dilshan/6ch-sound-processor/6ch-sound-fx-controller/src/resources.c

#include <gio/gio.h>

#if defined (__ELF__) && ( __GNUC__ > 2 || (__GNUC__ == 2 && __GNUC_MINOR__ >= 6))
# define SECTION __attribute__ ((section (".gresource.ch_tone_control"), aligned (8)))
#else
# define SECTION
#endif

#ifdef _MSC_VER
static const SECTION union { const guint8 data[22413]; const double alignment; void * const ptr;}  ch_tone_control_resource_data = { {
  0107, 0126, 0141, 0162, 0151, 0141, 0156, 0164, 0000, 0000, 0000, 0000, 0000, 0000, 0000, 0000, 
  0030, 0000, 0000, 0000, 0254, 0000, 0000, 0000, 0000, 0000, 0000, 0050, 0005, 0000, 0000, 0000, 
  0000, 0000, 0000, 0000, 0001, 0000, 0000, 0000, 0002, 0000, 0000, 0000, 0003, 0000, 0000, 0000, 
  0004, 0000, 0000, 0000, 0324, 0265, 0002, 0000, 0377, 0377, 0377, 0377, 0254, 0000, 0000, 0000, 
  0001, 0000, 0114, 0000, 0260, 0000, 0000, 0000, 0264, 0000, 0000, 0000, 0215, 0256, 0131, 0076, 
  0003, 0000, 0000, 0000, 0264, 0000, 0000, 0000, 0007, 0000, 0166, 0000, 0300, 0000, 0000, 0000, 
  0152, 0127, 0000, 0000, 0302, 0257, 0211, 0013, 0000, 0000, 0000, 0000, 0152, 0127, 0000, 0000, 
  0004, 0000, 0114, 0000, 0160, 0127, 0000, 0000, 0164, 0127, 0000, 0000, 0103, 0254, 0277, 0142, 
  0004, 0000, 0000, 0000, 0164, 0127, 0000, 0000, 0007, 0000, 0114, 0000, 0174, 0127, 0000, 0000, 
  0200, 0127, 0000, 0000, 0024, 0075, 0271, 0274, 0002, 0000, 0000, 0000, 0200, 0127, 0000, 0000, 
  0010, 0000, 0114, 0000, 0210, 0127, 0000, 0000, 0214, 0127, 0000, 0000, 0057, 0000, 0000, 0000, 
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
  "\000\031\164\105\130\164\123\157\146\164\167\141\162\145\000\167"
  "\167\167\056\151\156\153\163\143\141\160\145\056\157\162\147\233"
  "\356\074\032\000\000\040\000\111\104\101\124\170\234\354\235\167"
  "\170\134\305\271\270\337\355\105\132\365\056\331\226\254\342\046"
  "\313\105\256\340\202\301\066\275\044\100\022\002\111\110\041\044"
  "\067\067\355\246\367\033\322\313\057\275\020\222\134\040\215\164"
  "\010\020\212\301\306\275\127\331\226\055\313\226\255\336\173\335"
  "\172\176\177\034\213\030\133\147\316\356\352\154\223\367\175\236"
  "\175\300\072\263\063\263\273\347\373\316\314\067\137\321\161\165"
  "\220\016\254\003\126\003\163\201\122\040\011\110\001\164\021\234"
  "\127\234\310\043\001\175\300\000\120\013\124\003\333\201\255\100"
  "\167\344\246\025\147\262\350\201\273\201\177\003\156\344\037\072"
  "\376\212\277\374\175\271\201\347\201\067\043\337\113\161\142\004"
  "\035\360\166\240\206\310\337\104\361\327\324\170\235\002\336\106"
  "\234\250\247\030\170\215\310\337\060\361\327\324\174\155\006\212"
  "\210\023\225\334\203\274\227\213\364\115\022\177\115\355\127\057"
  "\360\046\246\010\206\110\117\100\043\076\002\374\006\260\105\172"
  "\042\161\246\074\126\340\055\300\010\260\073\302\163\231\064\123"
  "\101\001\174\036\370\036\161\153\176\234\360\241\003\066\000\116"
  "\140\147\204\347\062\051\142\135\150\336\013\374\232\000\076\207"
  "\303\142\142\132\262\035\207\305\104\212\325\114\222\335\206\121"
  "\037\067\362\136\255\110\100\357\310\030\275\243\116\316\164\366"
  "\323\067\352\014\364\355\357\001\236\010\305\334\302\101\054\053"
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
#endif /* !_MSC_VER */

static GStaticResource static_resource = { ch_tone_control_resource_data.data, sizeof (ch_tone_control_resource_data.data) - 1 /* nul terminator */, NULL, NULL, NULL };

G_MODULE_EXPORT
GResource *ch_tone_control_get_resource (void);
GResource *ch_tone_control_get_resource (void)
{
  return g_static_resource_get_resource (&static_resource);
}
/*
  If G_HAS_CONSTRUCTORS is true then the compiler support *both* constructors and
  destructors, in a usable way, including e.g. on library unload. If not you're on
  your own.

  Some compilers need #pragma to handle this, which does not work with macros,
  so the way you need to use this is (for constructors):

  #ifdef G_DEFINE_CONSTRUCTOR_NEEDS_PRAGMA
  #pragma G_DEFINE_CONSTRUCTOR_PRAGMA_ARGS(my_constructor)
  #endif
  G_DEFINE_CONSTRUCTOR(my_constructor)
  static void my_constructor(void) {
   ...
  }

*/

#ifndef __GTK_DOC_IGNORE__

#if  __GNUC__ > 2 || (__GNUC__ == 2 && __GNUC_MINOR__ >= 7)

#define G_HAS_CONSTRUCTORS 1

#define G_DEFINE_CONSTRUCTOR(_func) static void __attribute__((constructor)) _func (void);
#define G_DEFINE_DESTRUCTOR(_func) static void __attribute__((destructor)) _func (void);

#elif defined (_MSC_VER) && (_MSC_VER >= 1500)
/* Visual studio 2008 and later has _Pragma */

#include <stdlib.h>

#define G_HAS_CONSTRUCTORS 1

/* We do some weird things to avoid the constructors being optimized
 * away on VS2015 if WholeProgramOptimization is enabled. First we
 * make a reference to the array from the wrapper to make sure its
 * references. Then we use a pragma to make sure the wrapper function
 * symbol is always included at the link stage. Also, the symbols
 * need to be extern (but not dllexport), even though they are not
 * really used from another object file.
 */

/* We need to account for differences between the mangling of symbols
 * for x86 and x64/ARM/ARM64 programs, as symbols on x86 are prefixed
 * with an underscore but symbols on x64/ARM/ARM64 are not.
 */
#ifdef _M_IX86
#define G_MSVC_SYMBOL_PREFIX "_"
#else
#define G_MSVC_SYMBOL_PREFIX ""
#endif

#define G_DEFINE_CONSTRUCTOR(_func) G_MSVC_CTOR (_func, G_MSVC_SYMBOL_PREFIX)
#define G_DEFINE_DESTRUCTOR(_func) G_MSVC_DTOR (_func, G_MSVC_SYMBOL_PREFIX)

#define G_MSVC_CTOR(_func,_sym_prefix) \
  static void _func(void); \
  extern int (* _array ## _func)(void);              \
  int _func ## _wrapper(void) { _func(); g_slist_find (NULL,  _array ## _func); return 0; } \
  __pragma(comment(linker,"/include:" _sym_prefix # _func "_wrapper")) \
  __pragma(section(".CRT$XCU",read)) \
  __declspec(allocate(".CRT$XCU")) int (* _array ## _func)(void) = _func ## _wrapper;

#define G_MSVC_DTOR(_func,_sym_prefix) \
  static void _func(void); \
  extern int (* _array ## _func)(void);              \
  int _func ## _constructor(void) { atexit (_func); g_slist_find (NULL,  _array ## _func); return 0; } \
   __pragma(comment(linker,"/include:" _sym_prefix # _func "_constructor")) \
  __pragma(section(".CRT$XCU",read)) \
  __declspec(allocate(".CRT$XCU")) int (* _array ## _func)(void) = _func ## _constructor;

#elif defined (_MSC_VER)

#define G_HAS_CONSTRUCTORS 1

/* Pre Visual studio 2008 must use #pragma section */
#define G_DEFINE_CONSTRUCTOR_NEEDS_PRAGMA 1
#define G_DEFINE_DESTRUCTOR_NEEDS_PRAGMA 1

#define G_DEFINE_CONSTRUCTOR_PRAGMA_ARGS(_func) \
  section(".CRT$XCU",read)
#define G_DEFINE_CONSTRUCTOR(_func) \
  static void _func(void); \
  static int _func ## _wrapper(void) { _func(); return 0; } \
  __declspec(allocate(".CRT$XCU")) static int (*p)(void) = _func ## _wrapper;

#define G_DEFINE_DESTRUCTOR_PRAGMA_ARGS(_func) \
  section(".CRT$XCU",read)
#define G_DEFINE_DESTRUCTOR(_func) \
  static void _func(void); \
  static int _func ## _constructor(void) { atexit (_func); return 0; } \
  __declspec(allocate(".CRT$XCU")) static int (* _array ## _func)(void) = _func ## _constructor;

#elif defined(__SUNPRO_C)

/* This is not tested, but i believe it should work, based on:
 * http://opensource.apple.com/source/OpenSSL098/OpenSSL098-35/src/fips/fips_premain.c
 */

#define G_HAS_CONSTRUCTORS 1

#define G_DEFINE_CONSTRUCTOR_NEEDS_PRAGMA 1
#define G_DEFINE_DESTRUCTOR_NEEDS_PRAGMA 1

#define G_DEFINE_CONSTRUCTOR_PRAGMA_ARGS(_func) \
  init(_func)
#define G_DEFINE_CONSTRUCTOR(_func) \
  static void _func(void);

#define G_DEFINE_DESTRUCTOR_PRAGMA_ARGS(_func) \
  fini(_func)
#define G_DEFINE_DESTRUCTOR(_func) \
  static void _func(void);

#else

/* constructors not supported for this compiler */

#endif

#endif /* __GTK_DOC_IGNORE__ */

#ifdef G_HAS_CONSTRUCTORS

#ifdef G_DEFINE_CONSTRUCTOR_NEEDS_PRAGMA
#pragma G_DEFINE_CONSTRUCTOR_PRAGMA_ARGS(resource_constructor)
#endif
G_DEFINE_CONSTRUCTOR(resource_constructor)
#ifdef G_DEFINE_DESTRUCTOR_NEEDS_PRAGMA
#pragma G_DEFINE_DESTRUCTOR_PRAGMA_ARGS(resource_destructor)
#endif
G_DEFINE_DESTRUCTOR(resource_destructor)

#else
#warning "Constructor not supported on this compiler, linking in resources will not work"
#endif

static void resource_constructor (void)
{
  g_static_resource_init (&static_resource);
}

static void resource_destructor (void)
{
  g_static_resource_fini (&static_resource);
}
